seandonker/GRC22_ChargerShutdownPCB/CAD/3DModels/MC14081BDG.step

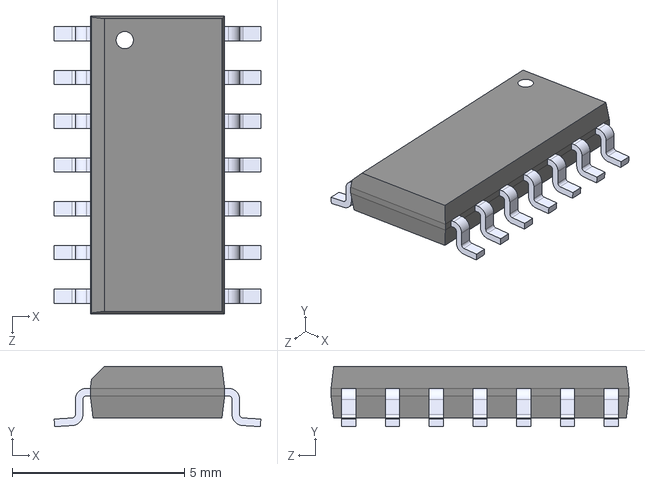
[picture p15: CAD file, 2023-11-27]
CAD/3DModels/MC14081BDG.step
6.00 x 1.75 x 8.65 mm
