seandonker/GRC22_ChargerShutdownPCB/CAD/3DModels/436500627.stp

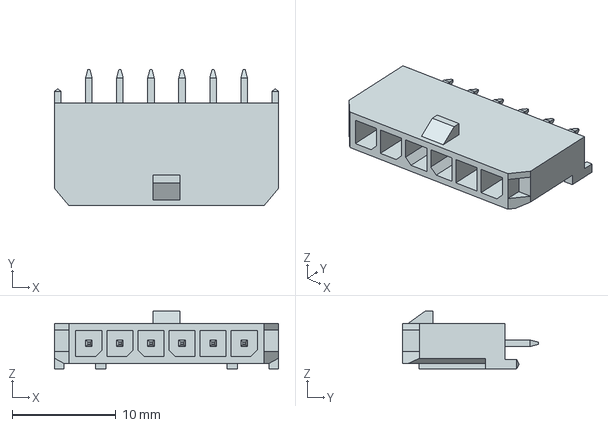
[picture p16: CAD file, 2023-11-27]
CAD/3DModels/436500627.stp
21.6 x 13.2 x 5.57 mm
