seandonker/GRC22_ChargerShutdownPCB/CAD/3DModels/436500227-2.stp

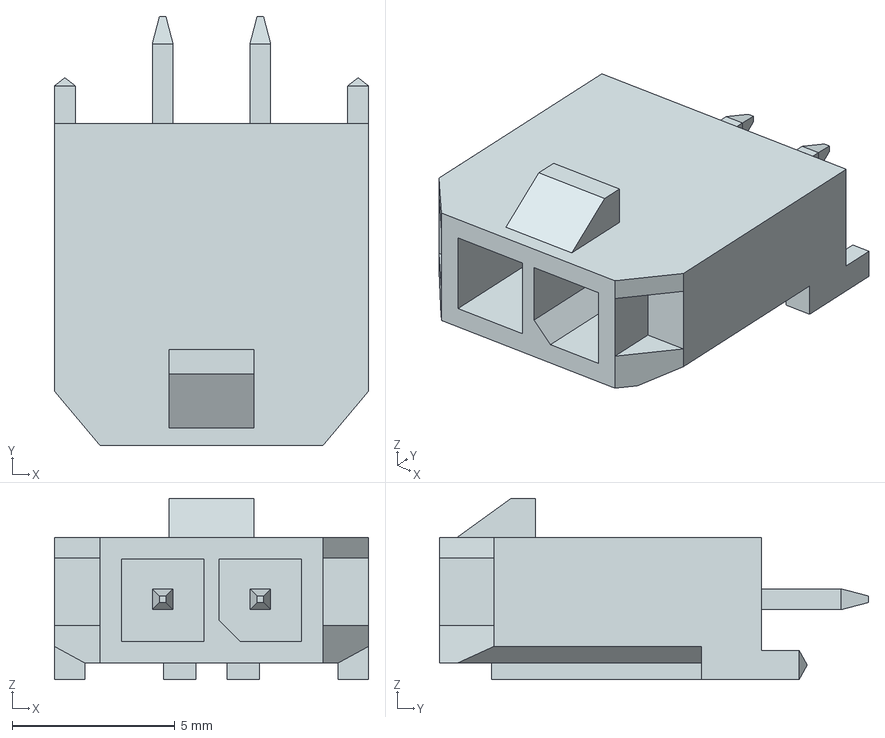
[picture p17: CAD file, 2023-11-27]
CAD/3DModels/436500227-2.stp
9.65 x 13.2 x 5.57 mm
