seandonker/GRC22_ChargerShutdownPCB/CAD/3DModels/0436500427--3DModel-STEP-231308.STEP

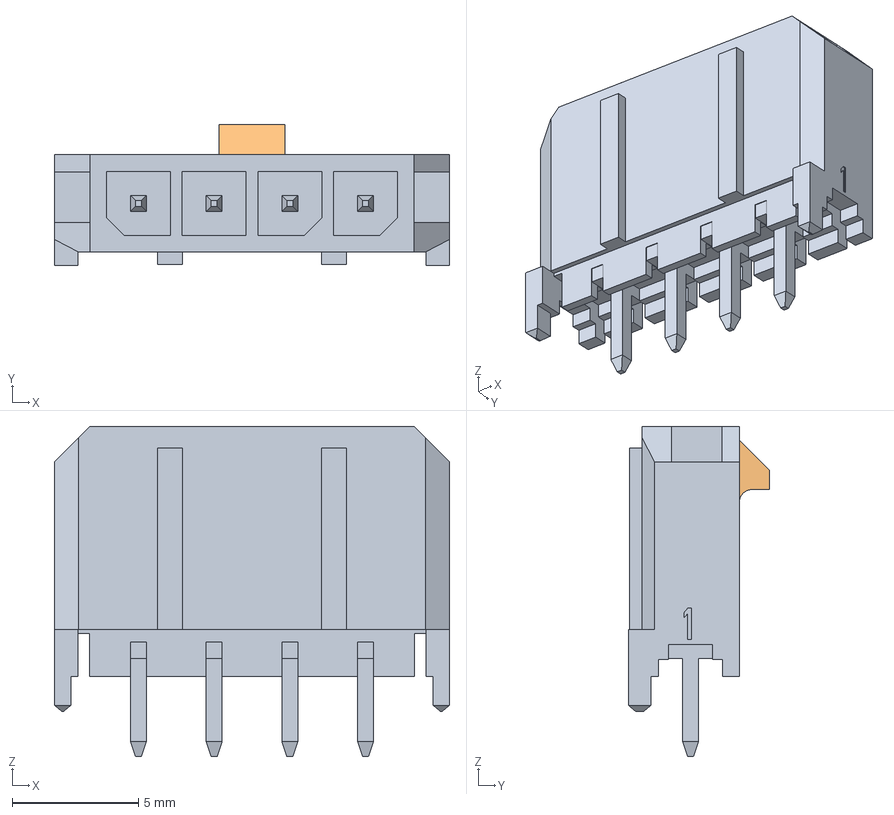
[picture p18: CAD file, 2023-11-27]
CAD/3DModels/0436500427--3DModel-STEP-231308.STEP
15.7 x 5.61 x 13.1 mm
